jeff-winn/nemesis-mod/sketches/Mainboard/Mainboard/src/FlywheelController.h

#ifndef FLYWHEEL_CONTROLLER_H
#define FLYWHEEL_CONTROLLER_H

#include <DualG2HighPowerMotorShield.h>
#include "MotorController.h"

// Defines the flywheel speeds available.
enum class FlywheelSpeed {
    Low = 1,
    Normal = 2,
    // WARNING: This value may cause physical bruising on the intended target, use with caution!
    Max = 255
};

// Defines the motors within the flywheel assembly.
enum class FlywheelMotor {
    Motor1 = 1,
    Motor2 = 2
};

// Provides a mechanism to control the flywheel assembly.
class FlywheelController : public MotorController {
    public:            
        FlywheelController();
        
        // Initializes the controller.
        void init() override;

        // Gets the current of the motor specified (in milliamps).
        unsigned int getMotorCurrentMilliamps(FlywheelMotor motor);

        // Gets the flywheel speed.
        FlywheelSpeed getSpeed();

        // Sets the flywheel speed.
        void setSpeed(FlywheelSpeed speed);

        // Sets the motor speed adjustment.
        void setMotorSpeedAdjustment(FlywheelMotor motor, float adjustment);

    protected:
        int calculateLimiterForSpeed(int speed);
        int calculateMotorSpeed(FlywheelMotor motor);
        float getMotorSpeedAdjustment(FlywheelMotor motor);
        int determineMotorMaximumSpeed();

        void updateDrivers();

        void onStart() override;
        void onStop() override;
        
    private:
        DualG2HighPowerMotorShield18v18 m_driver;

        FlywheelSpeed m_speed;
        int m_m1Speed;
        int m_m2Speed;
};

extern FlywheelController Flywheels;

#endif /* FLYWHEEL_CONTROLLER_H */
