jeff-winn/nemesis-mod/sketches/Mainboard/Mainboard/src/PusherController.h

#ifndef PUSHER_CONTROLLER_H
#define PUSHER_CONTROLLER_H

#include "hardware/G2HighPowerMotorShield.h"
#include "MotorController.h"

// Defines the pusher speeds (rate of fire) available.
enum class PusherSpeed {
    Normal = 1,
    Low = 2,
    Max = 255
};

// Provides a mechanism to control the pusher assembly.
class PusherController : public MotorController {
    public:
        PusherController();
        virtual ~PusherController() = default;

        // Initializes the controller.
        void init() override;

        // Gets the current of the motor specified (in milliamps).
        unsigned int getMotorCurrentMilliamps();

        // Gets the pusher speed.
        PusherSpeed getSpeed() const;

        // Sets the pusher speed.
        void setSpeed(PusherSpeed speed);

    protected:
        int calculateMotorSpeed() const;

        void onStart() override;
        void onStop() override;

        void updateDriver();
        
    private:
        G2HighPowerMotorShield18v17 m_driver;

        PusherSpeed m_speed;
        int m_m1speed;
};

extern PusherController Pusher;

#endif /* PUSHER_CONTROLLER_H */
