jeff-winn/nemesis-mod/sketches/Mainboard/Mainboard/src/MotorController.cpp

#include "MotorController.h"

void MotorController::init() {    
}

void MotorController::start() {
    if (m_isRunning) {
        return;
    }

    onStart();
    m_isRunning = true;
}

void MotorController::stop() {
    if (!m_isRunning) {
        return;
    }

    onStop();
    m_isRunning = false;
}

bool MotorController::isRunning() {
    return m_isRunning;
}
