jeff-winn/nemesis-mod/sketches/Bluetooth/Bluetooth/src/commands/I2cCommandFactory.cpp

#include <stddef.h>

#include "I2cCommandFactory.h"
#include "i2c/ResetCommand.h"
#include "i2c/StartAdvertisingCommand.h"
#include "i2c/SetCharacteristicCommand.h"
#include "i2c/SetNameCommand.h"
#include "i2c/SetPinCommand.h"
#include "i2c/SetTransmitCountCommand.h"
#include "../shared/Constants.h"

I2cCommandFactory I2cCommands = I2cCommandFactory();

I2cCommandFactory::I2cCommandFactory() {    
}

I2cCommandFactory::~I2cCommandFactory() {
}

Command* I2cCommandFactory::create(uint8_t type, uint8_t subtype) {
    switch (type) {
        case NRF52_CID_START_ADVERTISING:
            return new StartAdvertisingCommand();
        
        case NRF52_CID_RESET:
            return new ResetCommand();            
        
        case NRF52_CID_SET_CHARACTERISTIC:
            return new SetCharacteristicCommand(subtype);
        
        case NRF52_CID_SET_PIN:
            return new SetPinCommand();

        case NRF52_CID_SET_NAME:
            return new SetNameCommand();

        case NRF52_CID_SET_TRANSMIT_COUNT:
            return new SetTransmitCountCommand();
    }

    return nullptr;
}
