jeff-winn/nemesis-mod/sketches/Bluetooth/Bluetooth/src/commands/Command.cpp

#include "Command.h"

bool Command::validate() {
    return true;
}

void Command::execute(const uint8_t* data, const uint8_t len) {
    if (!validate()) {
        return;
    }

    executeImpl(data, len);
}
