jeff-winn/nemesis-mod/sketches/Mainboard/Mainboard/src/Command.cpp

#include "Command.h"

void Command::handle(const uint8_t* data, const uint16_t len) {
    if (!validate(data, len)) {
        return;
    }

    handleImpl(data, len);
}

bool Command::validate(const uint8_t* data, const uint16_t len) {
    return true;
}

bool Command::requiresAuthorization() {
    return true;
}
