jeff-winn/nemesis-mod/sketches/Mainboard/Mainboard/src/commands/ChangeConfigurationSettingCommand.h

#ifndef CHANGE_CONFIGURATION_SETTING_COMMAND_H
#define CHANGE_CONFIGURATION_SETTING_COMMAND_H

#include "ConfigurationCommand.h"

// Provides a command which changes configuration settings.
class ChangeConfigurationSettingCommand : public ConfigurationCommand {
    public:
        ChangeConfigurationSettingCommand(uint8_t subtype);

    protected:
        void handleImpl(const uint8_t* data, const uint16_t len) override;

        int getInt32ValueFromPacket(const uint8_t* data) const;
        byte getByteValueFromPacket(const uint8_t* data) const;
        float getFloatValueFromPacket(const uint8_t* data) const;

    private:
        uint8_t m_subtype;
};

#endif /* CHANGE_CONFIGURATION_SETTING_COMMAND_H */
