jeff-winn/nemesis-mod/sketches/Mainboard/Mainboard/src/commands/ConfigurationCommand.h

#ifndef CONFIGURATION_COMMAND_H
#define CONFIGURATION_COMMAND_H

#include "../Command.h"
#include "../ConfigurationSettings.h"

// Provides a base class for handling configuration commands.
class ConfigurationCommand : public Command {
};

#endif /* CONFIGURATION_COMMAND_H */
